rommarg/ultrasound_phantom/IMG_20260612_170545.jpg

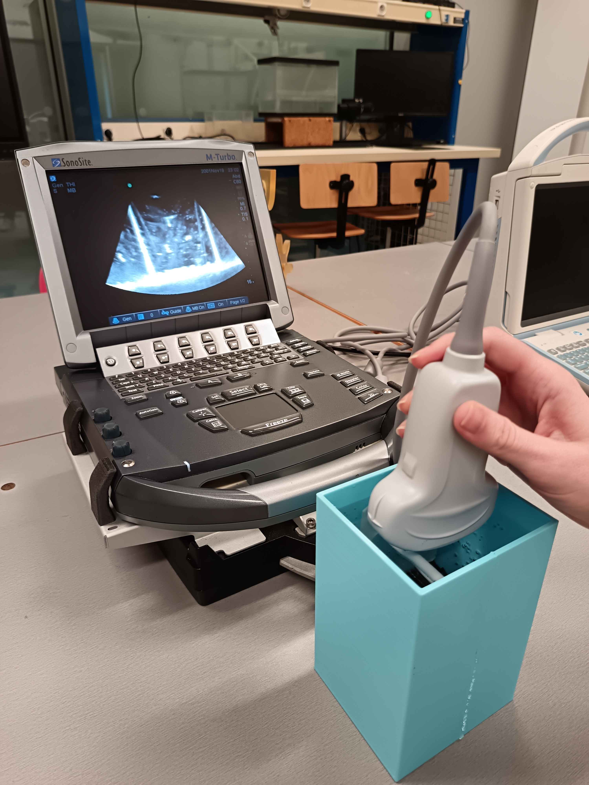
IMG_20260612_170545.jpg
